Tomas-Domas/PhotonPlay/demo materials/sin_lut_vivado_code/y_apple_offset.sv

module y_apple_offset #(
    parameter LUT_SIZE = 1024
)
(
    input clk,
    input we,
    input [$clog2(LUT_SIZE)-1:0] addr,
    input [11:0] di,
    output [11:0] dout
);

    reg [11:0] rom [LUT_SIZE-1:0];
    reg [11:0] dout;

    initial begin
		rom[0] = 12'd3584;
		rom[1] = 12'd640;
		rom[2] = 12'd3456;
		rom[3] = 12'd2560;
		rom[4] = 12'd2304;
		rom[5] = 12'd128;
		rom[6] = 12'd256;
		rom[7] = 12'd2304;
		rom[8] = 12'd2816;
		rom[9] = 12'd2176;
		rom[10] = 12'd3200;
		rom[11] = 12'd2560;
		rom[12] = 12'd3200;
		rom[13] = 12'd3072;
		rom[14] = 12'd2560;
		rom[15] = 12'd3328;
		rom[16] = 12'd1792;
		rom[17] = 12'd1152;
		rom[18] = 12'd1664;
		rom[19] = 12'd640;
		rom[20] = 12'd384;
		rom[21] = 12'd1792;
		rom[22] = 12'd2944;
		rom[23] = 12'd2688;
		rom[24] = 12'd384;
		rom[25] = 12'd256;
		rom[26] = 12'd1280;
		rom[27] = 12'd2432;
		rom[28] = 12'd3072;
		rom[29] = 12'd3200;
		rom[30] = 12'd1152;
		rom[31] = 12'd3968;
		rom[32] = 12'd512;
		rom[33] = 12'd256;
		rom[34] = 12'd3584;
		rom[35] = 12'd896;
		rom[36] = 12'd1024;
		rom[37] = 12'd2816;
		rom[38] = 12'd3456;
		rom[39] = 12'd3840;
		rom[40] = 12'd1408;
		rom[41] = 12'd640;
		rom[42] = 12'd640;
		rom[43] = 12'd512;
		rom[44] = 12'd3456;
		rom[45] = 12'd2944;
		rom[46] = 12'd1152;
		rom[47] = 12'd128;
		rom[48] = 12'd384;
		rom[49] = 12'd256;
		rom[50] = 12'd128;
		rom[51] = 12'd3584;
		rom[52] = 12'd0;
		rom[53] = 12'd3712;
		rom[54] = 12'd640;
		rom[55] = 12'd1536;
		rom[56] = 12'd128;
		rom[57] = 12'd3584;
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
		rom[1017] = 12'd1408;
		rom[1018] = 12'd2944;
		rom[1019] = 12'd2560;
		rom[1020] = 12'd2816;
		rom[1021] = 12'd640;
		rom[1022] = 12'd256;
		rom[1023] = 12'd0;

    end

    always @(posedge clk) begin
        if (we) rom[addr] <= di;
        dout <= rom[addr];
    end

endmodule
