Tomas-Domas/PhotonPlay/demo materials/sin_lut_vivado_code/x_win.sv

module x_win #(
    parameter LUT_SIZE = 154
)
(
    input clk,
    input we,
    input [$clog2(LUT_SIZE)-1:0] addr,
    input [11:0] di,
    output [11:0] dout
);

    reg [11:0] rom [LUT_SIZE-1:0];
    reg [11:0] dout;

    initial begin
		rom[0] = 12'd1212;
		rom[1] = 12'd1299;
		rom[2] = 12'd1386;
		rom[3] = 12'd1299;
		rom[4] = 12'd1299;
		rom[5] = 12'd1579;
		rom[6] = 12'd1666;
		rom[7] = 12'd1666;
		rom[8] = 12'd1579;
		rom[9] = 12'd1579;
		rom[10] = 12'd1491;
		rom[11] = 12'd1491;
		rom[12] = 12'd1579;
		rom[13] = 12'd1579;
		rom[14] = 12'd1841;
		rom[15] = 12'd1928;
		rom[16] = 12'd1928;
		rom[17] = 12'd1841;
		rom[18] = 12'd1754;
		rom[19] = 12'd1754;
		rom[20] = 12'd1841;
		rom[21] = 12'd2296;
		rom[22] = 12'd2383;
		rom[23] = 12'd2383;
		rom[24] = 12'd2296;
		rom[25] = 12'd2296;
		rom[26] = 12'd2296;
		rom[27] = 12'd2208;
		rom[28] = 12'd2208;
		rom[29] = 12'd2296;
		rom[30] = 12'd2558;
		rom[31] = 12'd2558;
		rom[32] = 12'd2488;
		rom[33] = 12'd2837;
		rom[34] = 12'd2837;
		rom[35] = 12'd2837;
		rom[36] = 12'd2663;
		rom[37] = 12'd2663;
		rom[38] = 12'd2750;
		rom[39] = 12'd2663;
		rom[40] = 12'd949;
		rom[41] = 12'd949;
		rom[42] = 12'd1037;
		rom[43] = 12'd949;
		rom[44] = 12'd1124;
		rom[45] = 12'd1124;
		rom[46] = 12'd949;
		rom[47] = 12'd1037;
		rom[48] = 12'd1124;
		rom[49] = 12'd1037;
		rom[50] = 12'd949;
		rom[51] = 12'd1037;
		rom[52] = 12'd1386;
		rom[53] = 12'd1229;
		rom[54] = 12'd1404;
		rom[55] = 12'd1404;
		rom[56] = 12'd1229;
		rom[57] = 12'd1229;
		rom[58] = 12'd1666;
		rom[59] = 12'd1666;
		rom[60] = 12'd1491;
		rom[61] = 12'd1491;
		rom[62] = 12'd1666;
		rom[63] = 12'd1491;
		rom[64] = 12'd1491;
		rom[65] = 12'd1666;
		rom[66] = 12'd1666;
		rom[67] = 12'd1491;
		rom[68] = 12'd1491;
		rom[69] = 12'd1946;
		rom[70] = 12'd1946;
		rom[71] = 12'd1754;
		rom[72] = 12'd1754;
		rom[73] = 12'd1946;
		rom[74] = 12'd1946;
		rom[75] = 12'd1754;
		rom[76] = 12'd1754;
		rom[77] = 12'd1946;
		rom[78] = 12'd1946;
		rom[79] = 12'd1754;
		rom[80] = 12'd1754;
		rom[81] = 12'd2208;
		rom[82] = 12'd2208;
		rom[83] = 12'd2033;
		rom[84] = 12'd2033;
		rom[85] = 12'd2208;
		rom[86] = 12'd2208;
		rom[87] = 12'd2033;
		rom[88] = 12'd2033;
		rom[89] = 12'd2208;
		rom[90] = 12'd2208;
		rom[91] = 12'd2033;
		rom[92] = 12'd2033;
		rom[93] = 12'd2750;
		rom[94] = 12'd2663;
		rom[95] = 12'd2558;
		rom[96] = 12'd2698;
		rom[97] = 12'd2610;
		rom[98] = 12'd2750;
		rom[99] = 12'd3012;
		rom[100] = 12'd3012;
		rom[101] = 12'd3012;
		rom[102] = 12'd2837;
		rom[103] = 12'd2837;
		rom[104] = 12'd2925;
		rom[105] = 12'd3012;
		rom[106] = 12'd3205;
		rom[107] = 12'd3205;
		rom[108] = 12'd3100;
		rom[109] = 12'd3205;
		rom[110] = 12'd3292;
		rom[111] = 12'd3117;
		rom[112] = 12'd1316;
		rom[113] = 12'd1316;
		rom[114] = 12'd1491;
		rom[115] = 12'd1491;
		rom[116] = 12'd1316;
		rom[117] = 12'd1491;
		rom[118] = 12'd1491;
		rom[119] = 12'd1316;
		rom[120] = 12'd1316;
		rom[121] = 12'd1666;
		rom[122] = 12'd1771;
		rom[123] = 12'd1771;
		rom[124] = 12'd1666;
		rom[125] = 12'd1579;
		rom[126] = 12'd1579;
		rom[127] = 12'd1666;
		rom[128] = 12'd1946;
		rom[129] = 12'd1946;
		rom[130] = 12'd1841;
		rom[131] = 12'd2051;
		rom[132] = 12'd1946;
		rom[133] = 12'd1858;
		rom[134] = 12'd2208;
		rom[135] = 12'd2208;
		rom[136] = 12'd2121;
		rom[137] = 12'd2296;
		rom[138] = 12'd2208;
		rom[139] = 12'd2121;
		rom[140] = 12'd2488;
		rom[141] = 12'd2575;
		rom[142] = 12'd2575;
		rom[143] = 12'd2488;
		rom[144] = 12'd2488;
		rom[145] = 12'd2400;
		rom[146] = 12'd2400;
		rom[147] = 12'd2488;
		rom[148] = 12'd2488;
		rom[149] = 12'd2837;
		rom[150] = 12'd2837;
		rom[151] = 12'd2837;
		rom[152] = 12'd2663;
		rom[153] = 12'd2663;
    end

    always @(posedge clk) begin
        if (we) rom[addr] <= di;
        dout <= rom[addr];
    end

endmodule
