Tomas-Domas/PhotonPlay/demo materials/sin_lut_vivado_code/y_win.sv

module y_win #(
    parameter LUT_SIZE = 154
)
(
    input clk,
    input we,
    input [$clog2(LUT_SIZE)-1:0] addr,
    input [11:0] di,
    output [11:0] dout
);

    reg [11:0] rom [LUT_SIZE-1:0];
    reg [11:0] dout;

    initial begin
		rom[0] = 12'd762;
		rom[1] = 12'd937;
		rom[2] = 12'd762;
		rom[3] = 12'd937;
		rom[4] = 12'd1111;
		rom[5] = 12'd1111;
		rom[6] = 12'd1024;
		rom[7] = 12'd849;
		rom[8] = 12'd762;
		rom[9] = 12'd1111;
		rom[10] = 12'd1041;
		rom[11] = 12'd849;
		rom[12] = 12'd762;
		rom[13] = 12'd1111;
		rom[14] = 12'd1111;
		rom[15] = 12'd1024;
		rom[16] = 12'd762;
		rom[17] = 12'd1111;
		rom[18] = 12'd762;
		rom[19] = 12'd1041;
		rom[20] = 12'd1111;
		rom[21] = 12'd1111;
		rom[22] = 12'd1041;
		rom[23] = 12'd762;
		rom[24] = 12'd1111;
		rom[25] = 12'd849;
		rom[26] = 12'd1111;
		rom[27] = 12'd762;
		rom[28] = 12'd1041;
		rom[29] = 12'd1111;
		rom[30] = 12'd1111;
		rom[31] = 12'd762;
		rom[32] = 12'd1111;
		rom[33] = 12'd1111;
		rom[34] = 12'd762;
		rom[35] = 12'd1111;
		rom[36] = 12'd762;
		rom[37] = 12'd1111;
		rom[38] = 12'd937;
		rom[39] = 12'd1111;
		rom[40] = 12'd1409;
		rom[41] = 12'd1758;
		rom[42] = 12'd1758;
		rom[43] = 12'd1583;
		rom[44] = 12'd1583;
		rom[45] = 12'd1409;
		rom[46] = 12'd1409;
		rom[47] = 12'd1409;
		rom[48] = 12'd1496;
		rom[49] = 12'd1583;
		rom[50] = 12'd1583;
		rom[51] = 12'd1758;
		rom[52] = 12'd1758;
		rom[53] = 12'd1583;
		rom[54] = 12'd1496;
		rom[55] = 12'd1409;
		rom[56] = 12'd1409;
		rom[57] = 12'd1758;
		rom[58] = 12'd1758;
		rom[59] = 12'd1671;
		rom[60] = 12'd1758;
		rom[61] = 12'd1583;
		rom[62] = 12'd1583;
		rom[63] = 12'd1583;
		rom[64] = 12'd1409;
		rom[65] = 12'd1409;
		rom[66] = 12'd1496;
		rom[67] = 12'd1409;
		rom[68] = 12'd1758;
		rom[69] = 12'd1758;
		rom[70] = 12'd1583;
		rom[71] = 12'd1583;
		rom[72] = 12'd1409;
		rom[73] = 12'd1409;
		rom[74] = 12'd1496;
		rom[75] = 12'd1409;
		rom[76] = 12'd1583;
		rom[77] = 12'd1583;
		rom[78] = 12'd1758;
		rom[79] = 12'd1671;
		rom[80] = 12'd1758;
		rom[81] = 12'd1758;
		rom[82] = 12'd1583;
		rom[83] = 12'd1583;
		rom[84] = 12'd1409;
		rom[85] = 12'd1409;
		rom[86] = 12'd1496;
		rom[87] = 12'd1409;
		rom[88] = 12'd1583;
		rom[89] = 12'd1583;
		rom[90] = 12'd1758;
		rom[91] = 12'd1671;
		rom[92] = 12'd1758;
		rom[93] = 12'd1758;
		rom[94] = 12'd1409;
		rom[95] = 12'd1758;
		rom[96] = 12'd1583;
		rom[97] = 12'd1583;
		rom[98] = 12'd1758;
		rom[99] = 12'd1758;
		rom[100] = 12'd1409;
		rom[101] = 12'd1758;
		rom[102] = 12'd1409;
		rom[103] = 12'd1758;
		rom[104] = 12'd1583;
		rom[105] = 12'd1758;
		rom[106] = 12'd1758;
		rom[107] = 12'd1583;
		rom[108] = 12'd1409;
		rom[109] = 12'd1583;
		rom[110] = 12'd1409;
		rom[111] = 12'd1758;
		rom[112] = 12'd2038;
		rom[113] = 12'd2388;
		rom[114] = 12'd2388;
		rom[115] = 12'd2300;
		rom[116] = 12'd2213;
		rom[117] = 12'd2125;
		rom[118] = 12'd2038;
		rom[119] = 12'd2038;
		rom[120] = 12'd2388;
		rom[121] = 12'd2388;
		rom[122] = 12'd2300;
		rom[123] = 12'd2038;
		rom[124] = 12'd2388;
		rom[125] = 12'd2300;
		rom[126] = 12'd2038;
		rom[127] = 12'd2388;
		rom[128] = 12'd2388;
		rom[129] = 12'd2038;
		rom[130] = 12'd2038;
		rom[131] = 12'd2038;
		rom[132] = 12'd2038;
		rom[133] = 12'd2388;
		rom[134] = 12'd2388;
		rom[135] = 12'd2038;
		rom[136] = 12'd2038;
		rom[137] = 12'd2038;
		rom[138] = 12'd2038;
		rom[139] = 12'd2388;
		rom[140] = 12'd2388;
		rom[141] = 12'd2300;
		rom[142] = 12'd2125;
		rom[143] = 12'd2038;
		rom[144] = 12'd2388;
		rom[145] = 12'd2300;
		rom[146] = 12'd2125;
		rom[147] = 12'd2038;
		rom[148] = 12'd2388;
		rom[149] = 12'd2388;
		rom[150] = 12'd2038;
		rom[151] = 12'd2388;
		rom[152] = 12'd2038;
		rom[153] = 12'd2388;
    end

    always @(posedge clk) begin
        if (we) rom[addr] <= di;
        dout <= rom[addr];
    end

endmodule
