Tomas-Domas/PhotonPlay/demo materials/sin_lut_vivado_code/x_start.sv

module x_start #(
    parameter LUT_SIZE = 169
)
(
    input clk,
    input we,
    input [$clog2(LUT_SIZE)-1:0] addr,
    input [11:0] di,
    output [11:0] dout
);

    reg [11:0] rom [LUT_SIZE-1:0];
    reg [11:0] dout;

    initial begin
		rom[0] = 12'd564;
		rom[1] = 12'd930;
		rom[2] = 12'd930;
		rom[3] = 12'd674;
		rom[4] = 12'd674;
		rom[5] = 12'd930;
		rom[6] = 12'd930;
		rom[7] = 12'd564;
		rom[8] = 12'd564;
		rom[9] = 12'd821;
		rom[10] = 12'd821;
		rom[11] = 12'd564;
		rom[12] = 12'd564;
		rom[13] = 12'd1589;
		rom[14] = 12'd1589;
		rom[15] = 12'd1479;
		rom[16] = 12'd1479;
		rom[17] = 12'd1333;
		rom[18] = 12'd1186;
		rom[19] = 12'd1186;
		rom[20] = 12'd1333;
		rom[21] = 12'd1333;
		rom[22] = 12'd1442;
		rom[23] = 12'd2357;
		rom[24] = 12'd2101;
		rom[25] = 12'd1845;
		rom[26] = 12'd1954;
		rom[27] = 12'd2101;
		rom[28] = 12'd2247;
		rom[29] = 12'd2979;
		rom[30] = 12'd2723;
		rom[31] = 12'd2979;
		rom[32] = 12'd2979;
		rom[33] = 12'd2723;
		rom[34] = 12'd2723;
		rom[35] = 12'd2613;
		rom[36] = 12'd2613;
		rom[37] = 12'd2723;
		rom[38] = 12'd2723;
		rom[39] = 12'd2832;
		rom[40] = 12'd3600;
		rom[41] = 12'd3600;
		rom[42] = 12'd3344;
		rom[43] = 12'd3344;
		rom[44] = 12'd3600;
		rom[45] = 12'd3600;
		rom[46] = 12'd3344;
		rom[47] = 12'd3344;
		rom[48] = 12'd3600;
		rom[49] = 12'd3600;
		rom[50] = 12'd3235;
		rom[51] = 12'd3235;
		rom[52] = 12'd455;
		rom[53] = 12'd455;
		rom[54] = 12'd564;
		rom[55] = 12'd455;
		rom[56] = 12'd674;
		rom[57] = 12'd674;
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
		rom[162] = 12'd2613;
		rom[163] = 12'd2613;
		rom[164] = 12'd3125;
		rom[165] = 12'd3125;
		rom[166] = 12'd3125;
		rom[167] = 12'd2869;
		rom[168] = 12'd2869;
    end

    always @(posedge clk) begin
        if (we) rom[addr] <= di;
        dout <= rom[addr];
    end

endmodule
