Tomas-Domas/PhotonPlay/demo materials/sin_lut_vivado_code/borderx_rom.sv

module borderx_rom #(
    parameter LUT_SIZE = 14
)
(
    input clk,
    input we,
    input [$clog2(LUT_SIZE)-1:0] addr,
    input [11:0] di,
    output [11:0] dout
);

    reg [11:0] rom [LUT_SIZE-1:0];
    reg [11:0] dout;

    initial begin
		rom[0] = 12'd4095;
        rom[1] = 12'd4095; 
		rom[2] = 12'd2047;//
		rom[3] = 12'd0;
        rom[4] = 12'd0;
		rom[5] = 12'd0;//
		rom[6] = 12'd0;
        rom[7] = 12'd0;
		rom[8] = 12'd2047;//
		rom[9] = 12'd4095;
        rom[10] = 12'd4095;
		rom[11] = 12'd4095;//
        rom[12] = 12'd4095;
        rom[13] = 12'd4095;
    end

    always @(posedge clk) begin
        if (we) rom[addr] <= di;
        dout <= rom[addr];
    end

endmodule
